astromik/celovka/krabicka-3d/krab6-b.gif

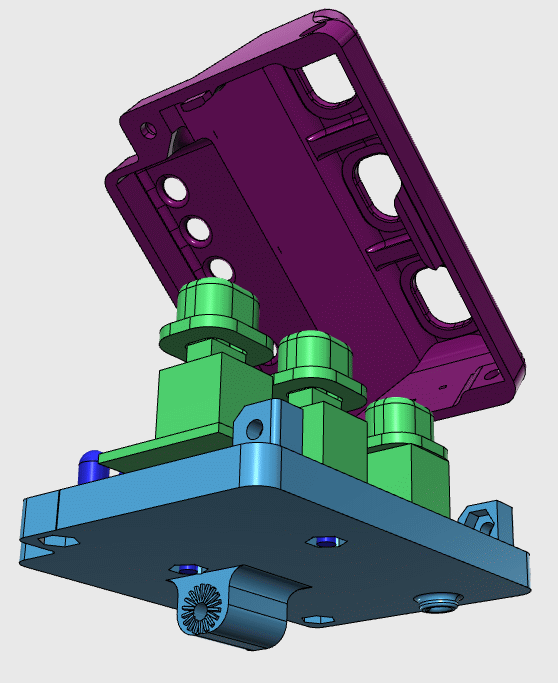
krabicka-3d/krab6-b.gif
