astromik/celovka/krabicka-3d/krabicka6ani.gif

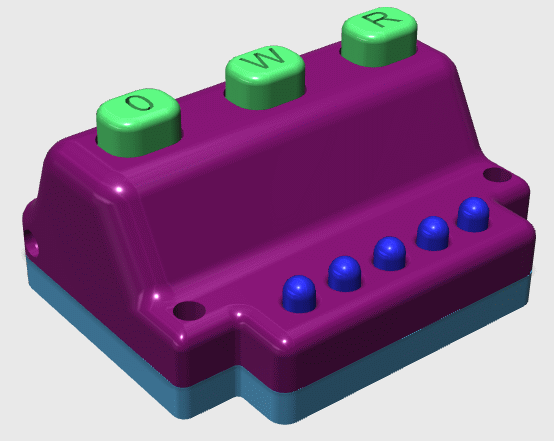
krabicka-3d/krabicka6ani.gif
