astromik/celovka/pcb/pcb_bottom.png

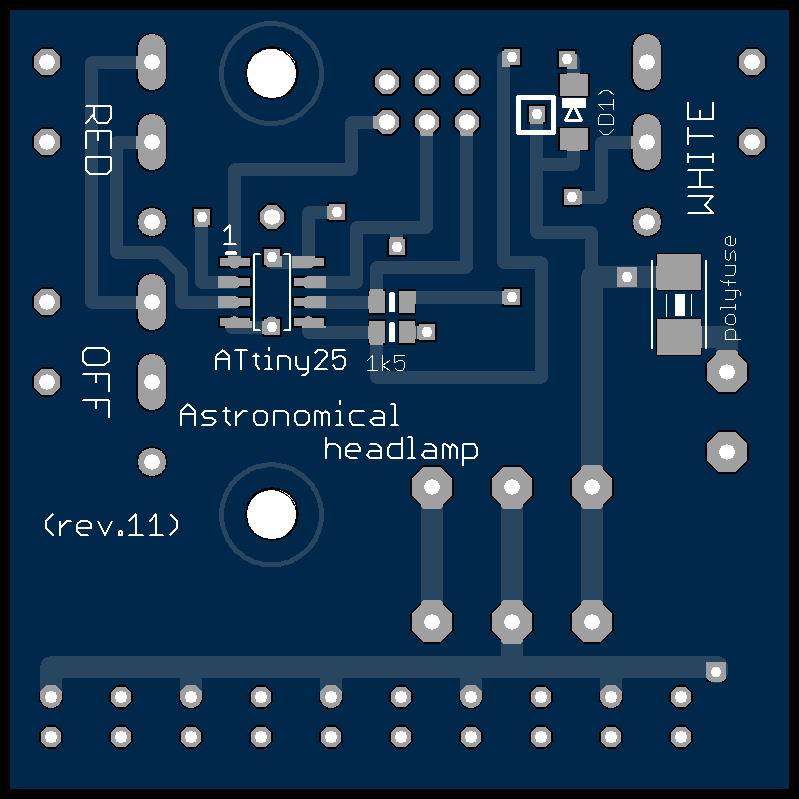
pcb/pcb_bottom.png
