astromik/celovka/schema/celovka-schema.gif

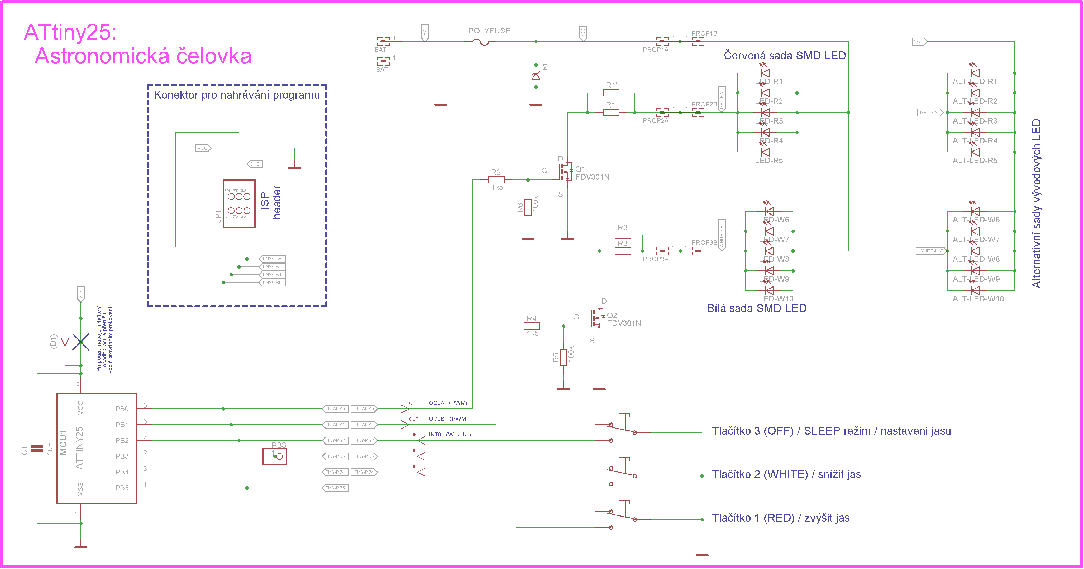
schema/celovka-schema.gif
