astromik/celovka/ArduinoIDE_setup/avrdudess.gif

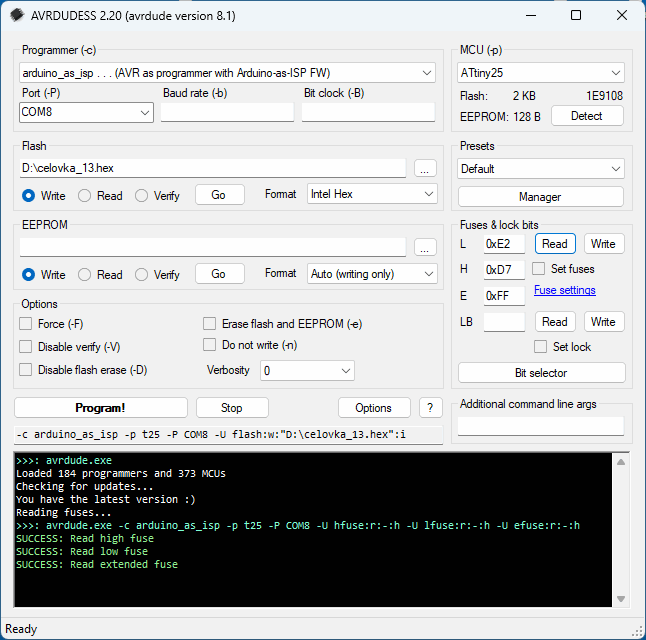
ArduinoIDE_setup/avrdudess.gif
