astromik/celovka/ArduinoIDE_setup/ide1.gif

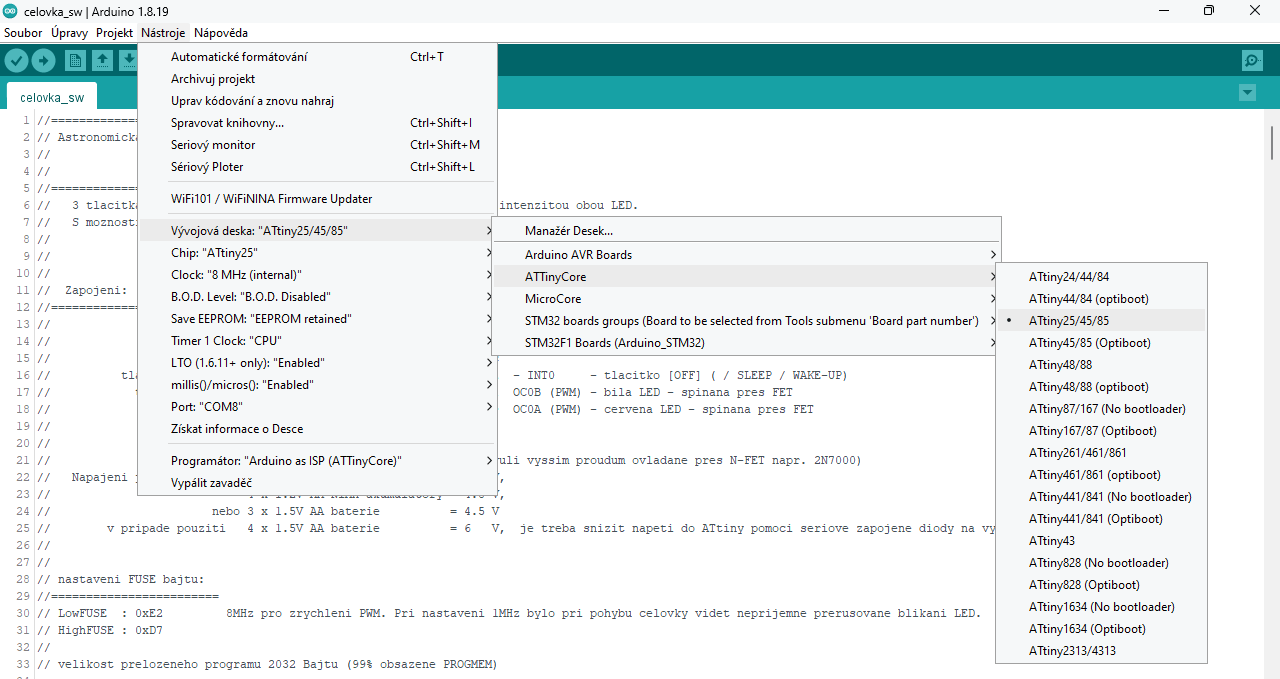
ArduinoIDE_setup/ide1.gif
