astromik/celovka/ArduinoIDE_setup/ide2.gif

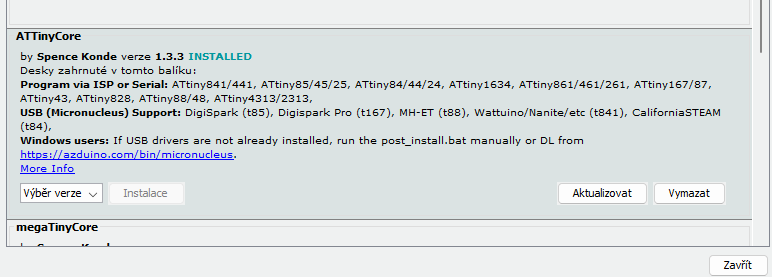
ArduinoIDE_setup/ide2.gif
