astromik/celovka/ArduinoIDE_setup/ide3.gif

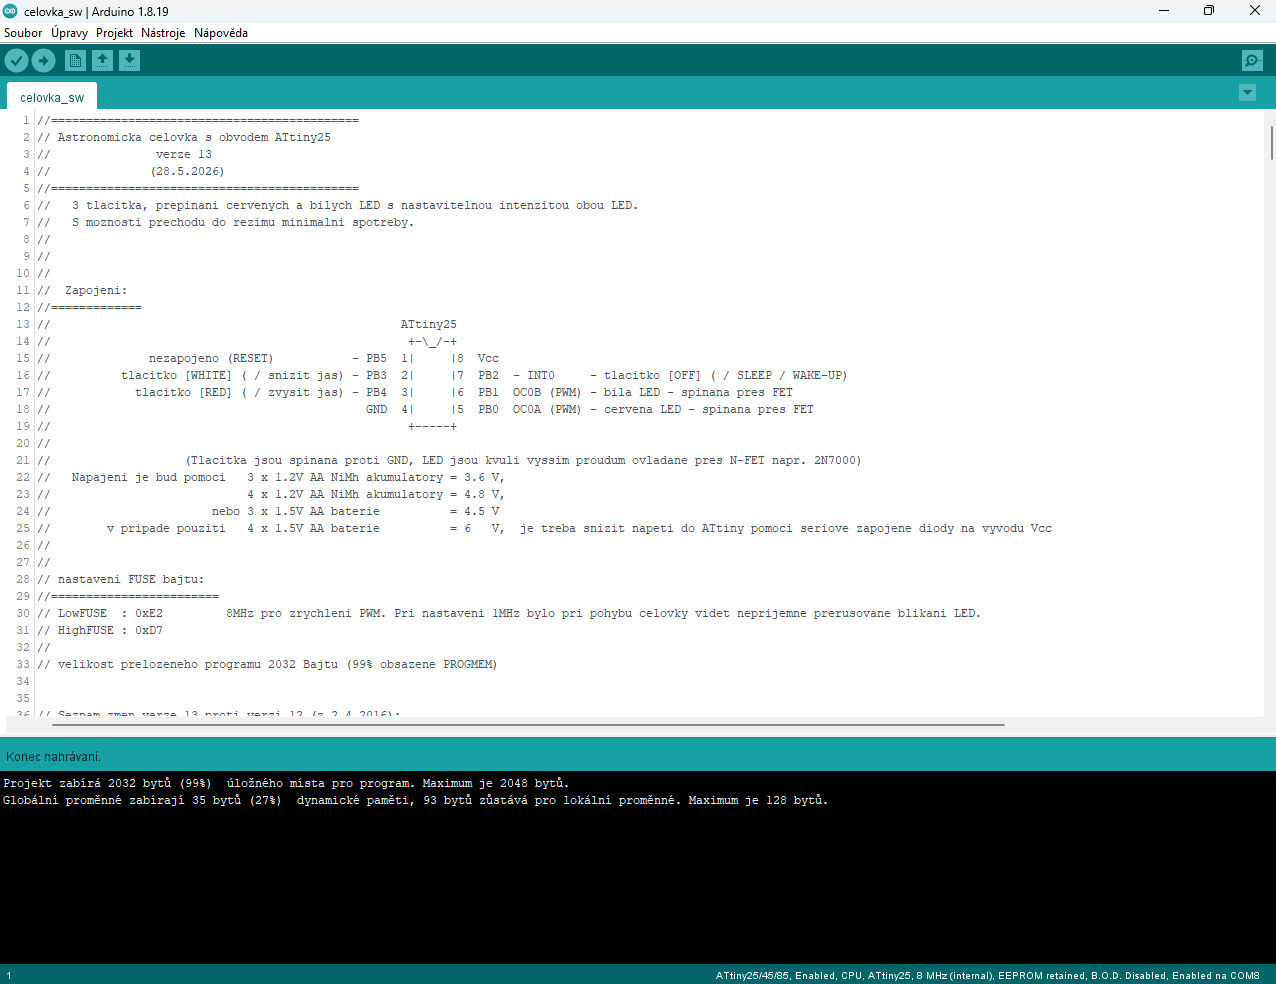
ArduinoIDE_setup/ide3.gif
